Supermanuu/BatterySwitcher/doc/mounting/img/connecting-connector.jpg

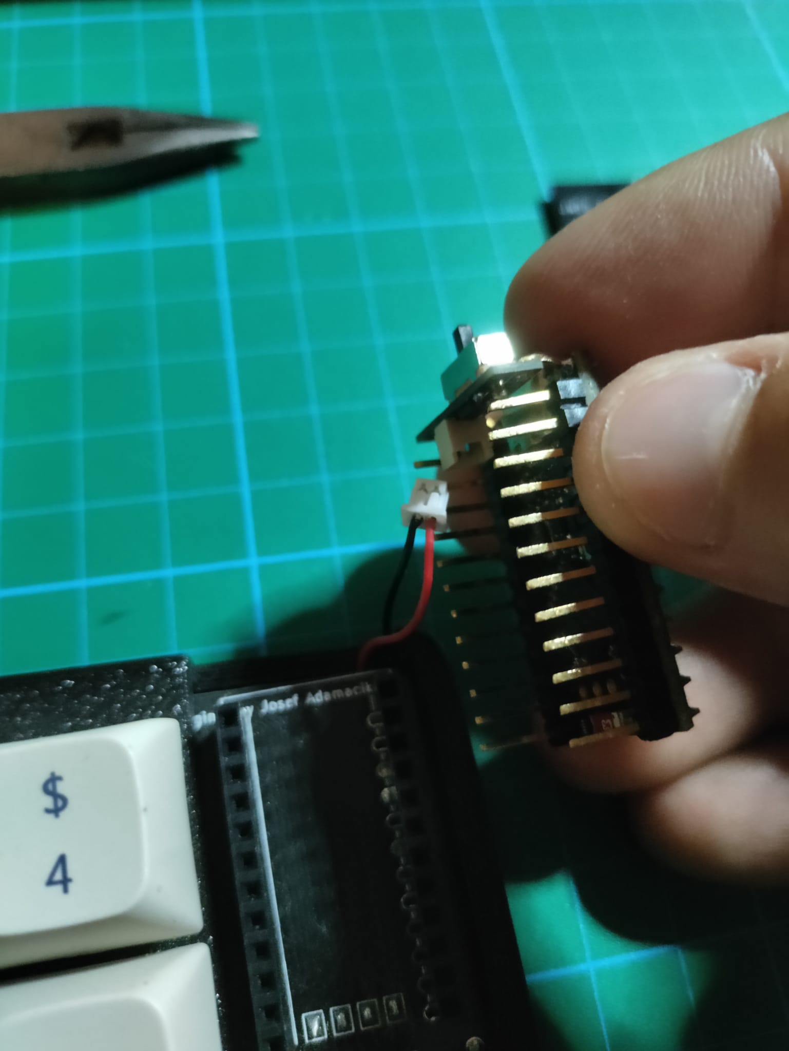
doc/mounting/img/connecting-connector.jpg
