Supermanuu/BatterySwitcher/doc/mounting/img/pins.jpg

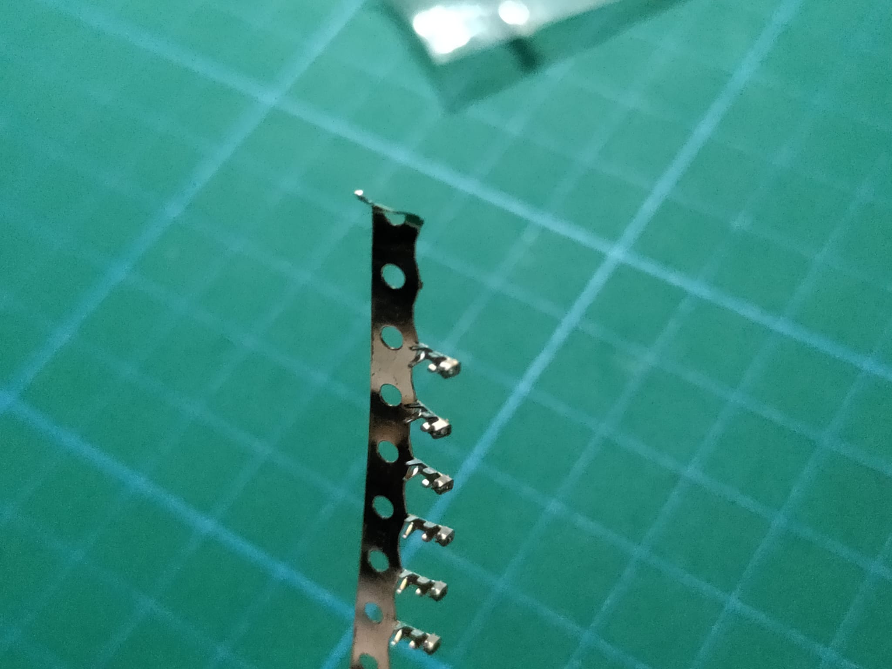
doc/mounting/img/pins.jpg
